nrivard/n8-Bit/PCB/viaduct/viaduct.kicad_pcb

## KiCad design PCB/viaduct/viaduct.kicad_pcb (2022-01-05)

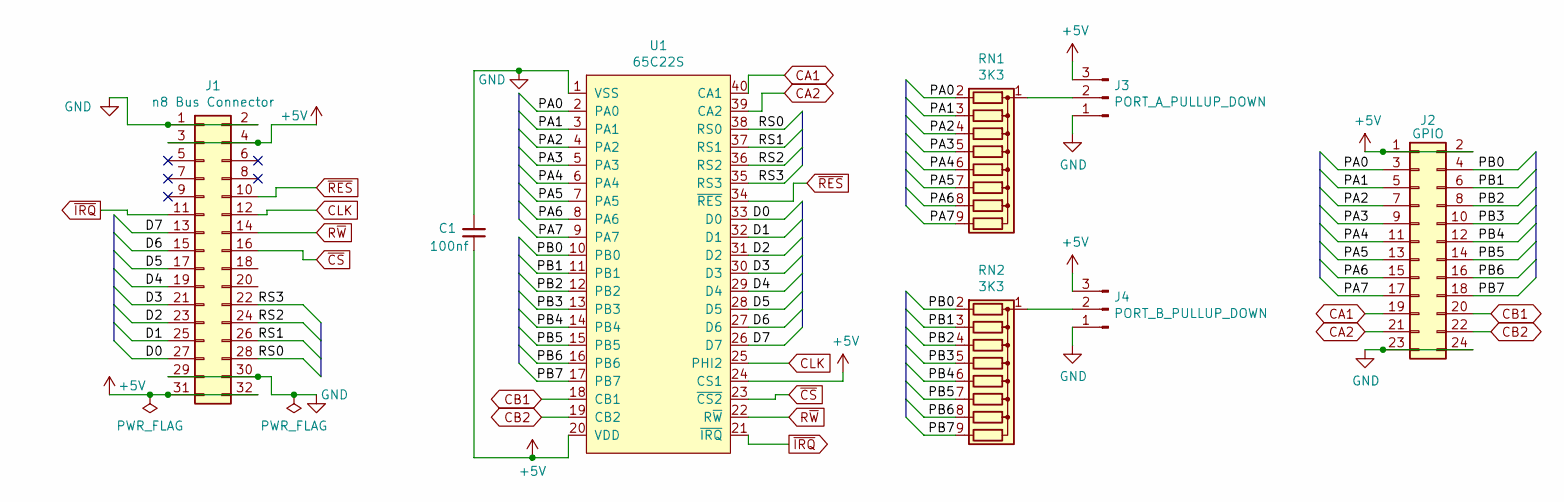
[picture p27: schematic viaduct.kicad_sch]

Parts:
C1: 100nf; C_Disc_D5.0mm_W2.5mm_P2.50mm
J1: n8 Bus Connector; PinHeader_2x16_P2.54mm_Horizontal
J2: GPIO; PinSocket_2x12_P2.54mm_Horizontal
J3: PORT_A_PULLUP_DOWN; PinHeader_1x03_P2.54mm_Vertical
J4: PORT_B_PULLUP_DOWN; PinHeader_1x03_P2.54mm_Vertical
RN1, RN2: 3K3; R_Array_SIP9
U1: 65C22S; DIP-40_W15.24mm_Socket

Connections:
+5V: C1.1, J1.3, J1.4, J1.31, J1.32, J2.1, J2.2, J3.3, J4.3, U1.20 (VDD), U1.24 (CS1)
/D0: J1.27, U1.33 (D0)
/D1: J1.25, U1.32 (D1)
/D2: J1.23, U1.31 (D2)
/D3: J1.21, U1.30 (D3)
/D4: J1.19, U1.29 (D4)
/D5: J1.17, U1.28 (D5)
/D6: J1.15, U1.27 (D6)
/D7: J1.13, U1.26 (D7)
/PA0: J2.3, RN1.2 (R1), U1.2 (PA0)
/PA1: J2.5, RN1.3 (R2), U1.3 (PA1)
/PA2: J2.7, RN1.4 (R3), U1.4 (PA2)
/PA3: J2.9, RN1.5 (R4), U1.5 (PA3)
/PA4: J2.11, RN1.6 (R5), U1.6 (PA4)
/PA5: J2.13, RN1.7 (R6), U1.7 (PA5)
/PA6: J2.15, RN1.8 (R7), U1.8 (PA6)
/PA7: J2.17, RN1.9 (R8), U1.9 (PA7)
/PB0: J2.4, RN2.2 (R1), U1.10 (PB0)
/PB1: J2.6, RN2.3 (R2), U1.11 (PB1)
/PB2: J2.8, RN2.4 (R3), U1.12 (PB2)
/PB3: J2.10, RN2.5 (R4), U1.13 (PB3)
/PB4: J2.12, RN2.6 (R5), U1.14 (PB4)
/PB5: J2.14, RN2.7 (R6), U1.15 (PB5)
/PB6: J2.16, RN2.8 (R7), U1.16 (PB6)
/PB7: J2.18, RN2.9 (R8), U1.17 (PB7)
/RS0: J1.28, U1.38 (RS0)
/RS1: J1.26, U1.37 (RS1)
/RS2: J1.24, U1.36 (RS2)
/RS3: J1.22, U1.35 (RS3)
CA1: J2.19, U1.40 (CA1)
CA2: J2.21, U1.39 (CA2)
CB1: J2.20, U1.18 (CB1)
CB2: J2.22, U1.19 (CB2)
CLK: J1.12, U1.25 (PHI2)
GND: C1.2, J1.1, J1.2, J1.29, J1.30, J2.23, J2.24, J3.1, J4.1, U1.1 (VSS)
unnamed: J3.2, RN1.1 (common)
unnamed: J4.2, RN2.1 (common)
R~W: J1.14, U1.22 (R~W)
~CS: J1.16, U1.23 (~CS2)
~IRQ: J1.11, U1.21 (~IRQ)
~RES: J1.10, U1.34 (~RES)

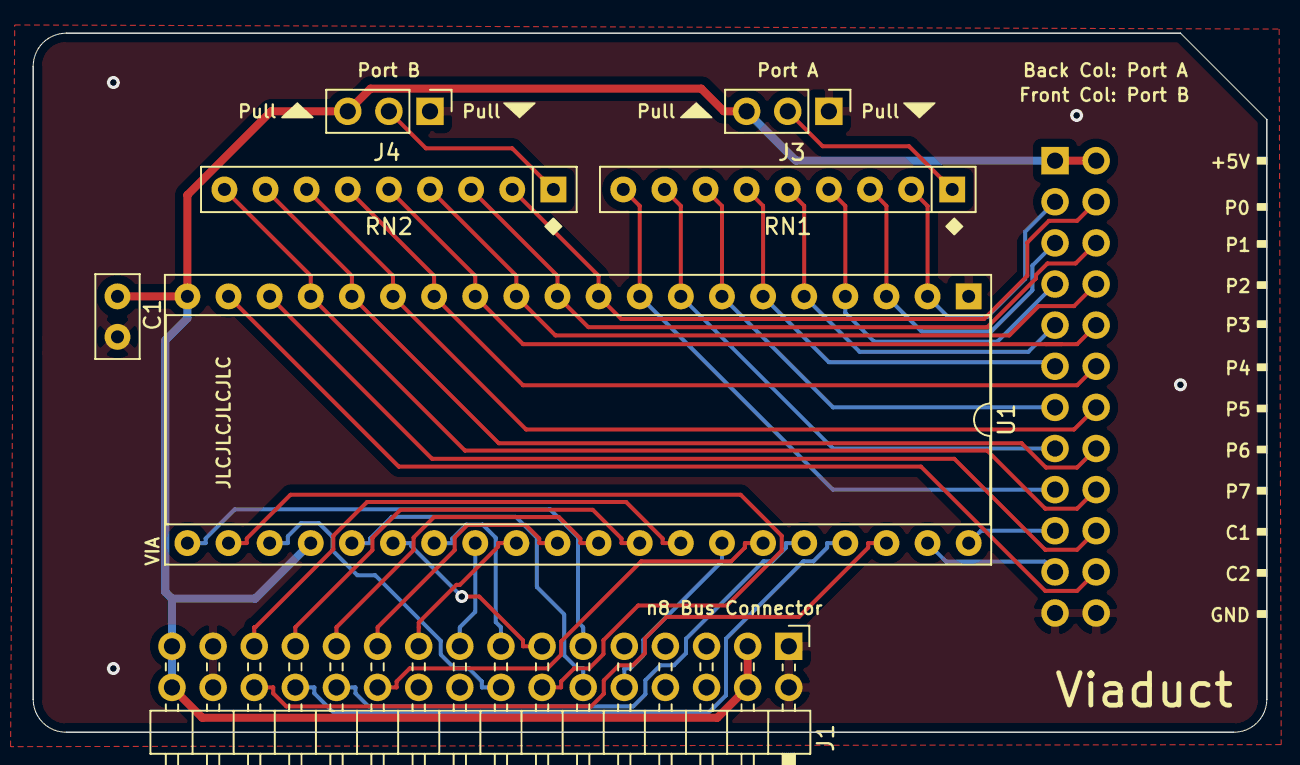
[picture p28: board viaduct.kicad_pcb from above]

Board: 2 copper layers, 76.2 x 43.2 mm, 8 parts (1 on the bottom side), 41 nets.
